qb-creates/LedCube/555LedCube/555LedCube/Cage_Animation.asm

/*
 * Cage_Animation.asm
 *
 *  Created: 4/10/2017 11:21:32 AM
 *   Author: qbake_0
 */ 
 /////////////////////////////////////////////////////////////////////////////////////////////////////////////////////////////////////
Cage:																																;
	ldi Xh, 0x00 ldi Xl, 0xAE																										;
	ldi Byte_1, 0x00 ST X+, Byte_1	ldi Byte_2, 0x00 ST X+, Byte_2	ldi Byte_3, 0x00 ST X+, Byte_3 ldi Byte_4, 0x00 ST X+, Byte_4	;
	ldi Byte_1, 0x00 ST X+, Byte_1	ldi Byte_2, 0x00 ST X+, Byte_2	ldi Byte_3, 0x00 ST X+, Byte_3 ldi Byte_4, 0x00 ST X+, Byte_4	;
	ldi Byte_1, 0x00 ST X+, Byte_1	ldi Byte_2, 0x00 ST X+, Byte_2	ldi Byte_3, 0x00 ST X+, Byte_3 ldi Byte_4, 0x00 ST X+, Byte_4	;
	ldi Byte_1, 0x00 ST X+, Byte_1	ldi Byte_2, 0x00 ST X+, Byte_2	ldi Byte_3, 0x00 ST X+, Byte_3 ldi Byte_4, 0x00 ST X+, Byte_4	;
	ldi Byte_1, 0x00 ST X+, Byte_1	ldi Byte_2, 0x00 ST X+, Byte_2	ldi Byte_3, 0x00 ST X+, Byte_3 ldi Byte_4, 0x00 ST X+, Byte_4	;
	ldi temp_3, 255 ldi counter, 1 call bright																						;
ldi Subtraction4, 0xBE																												;
Cage_loop:																															;
	ldi Xh, 0x00 Mov Xl, Subtraction4 																								;
	ldi Byte_1, 0x01 ST X+, Byte_1	ldi Byte_2, 0x00 ST X+, Byte_2	ldi Byte_3, 0x00 ST X+, Byte_3 ldi Byte_4, 0x00 ST X+, Byte_4	;
	ldi temp_3, 185 ldi counter, 12 call bright																						;
																																	;
	ldi Xh, 0x00 Mov Xl, Subtraction4 																								;
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
	ldi temp_3, 185 ldi counter, 15 call bright																						;
	RET																																;
/////////////////////////////////////////////////////////////////////////////////////////////////////////////////////////////////////
