qb-creates/LedCube/555LedCube/555LedCube/Expand_Animation.asm

/*
 * Expand_Animation.asm
 *
 *  Created: 4/10/2017 11:10:27 AM
 *   Author: qbake_0
 */ 
 ////////////////////////////////////////////////////////////////////////////////////////////////////////////////////////////////
 Expand_4:																														;
			ldi Xh, 0x00																										;
			ldi Xl, 0xAE																										;
			ldi temp, 0x10 ST X+, temp	ldi temp, 0x00 ST X+, temp	ldi temp, 0x00 ST X+, temp	ldi temp, 0x00 ST X+, temp      ;
			ldi temp, 0x00 ST X+, temp	ldi temp, 0x00 ST X+, temp	ldi temp, 0x00 ST X+, temp	ldi temp, 0x00 ST X+, temp      ;
			ldi temp, 0x00 ST X+, temp	ldi temp, 0x00 ST X+, temp	ldi temp, 0x00 ST X+, temp	ldi temp, 0x00 ST X+, temp      ;
			ldi temp, 0x00 ST X+, temp	ldi temp, 0x00 ST X+, temp	ldi temp, 0x00 ST X+, temp	ldi temp, 0x00 ST X+, temp      ;
			ldi temp, 0x00 ST X+, temp	ldi temp, 0x00 ST X+, temp	ldi temp, 0x00 ST X+, temp	ldi temp, 0x00 ST X+, temp      ;
			ldi temp_3, 115 ldi counter, 15 call bright																			;
																																;
			ldi Xh, 0x00																										;
			ldi Xl, 0xAE																										;
			ldi temp, 0x18 ST X+, temp	ldi temp, 0x03 ST X+, temp	ldi temp, 0x00 ST X+, temp	ldi temp, 0x00 ST X+, temp      ;
			ldi temp, 0x18 ST X+, temp	ldi temp, 0x03 ST X+, temp	ldi temp, 0x00 ST X+, temp	ldi temp, 0x00 ST X+, temp      ;
			ldi temp, 0x00 ST X+, temp	ldi temp, 0x00 ST X+, temp	ldi temp, 0x00 ST X+, temp	ldi temp, 0x00 ST X+, temp      ;
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
			ldi temp_3, 115 ldi counter, 10 call bright																			;
																																;
			RET																													;
////////////////////////////////////////////////////////////////////////////////////////////////////////////////////////////////;
