qb-creates/LedCube/555LedCube/555LedCube/Explode_Animation.asm

/*
 * AsmFile3.asm
 *
 *  Created: 4/10/2017 1:16:20 AM
 *   Author: qbake_0
 */ 
 Explode:																																																														;
																									;																																							;
	ldi Xh, 0x00 ldi Xl, 0xBE																																																									;
	ldi Byte_1, 0b00000000 EOR Byte_1, Subtraction4 ST X+, Byte_1	ldi Byte_2, 0b00000000 EOR Byte_2, Subtraction4 ST X+, Byte_2	ldi Byte_3, 0b00000000 EOR Byte_3, Subtraction4 ST X+, Byte_3 ldi Byte_4, 0b00000001 EOR Byte_4, Subtraction4 ST X+, Byte_4	;
	ldi temp_3, 255 ldi counter, 3 call bright																																																				;
																																																																;
	ldi Xh, 0x00 ldi Xl, 0xB6																																																									;
	ldi Byte_1, 0b00000100 eor Byte_1, Subtraction4 ST X+, Byte_1   ldi Byte_2, 0b00000000 eor Byte_2, Subtraction4 ST X+, Byte_2	ldi Byte_3, 0b00000000 eor Byte_3, Subtraction4 ST X+, Byte_3 ldi Byte_4, 0b00000000 eor Byte_4, Subtraction4 ST X+, Byte_4	;
	ldi temp_3, 255 ldi counter, 3 call bright																																																				;
																																																																;
	ldi Xh, 0x00 ldi Xl, 0xBA																																																									;
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
	ldi temp_3, 255 ldi counter, 3 call bright																													;
																																								;
	ldi Xh, 0x00 ldi Xl, 0xB2																																	;
	ldi Byte_1, 0b11111111 eor Byte_1, Subtraction4 ST X+, Byte_1	ldi Byte_2, 0b11111111 eor Byte_2, Subtraction4 ST X+, Byte_2	ldi Byte_3, 0b11111111 eor Byte_3, Subtraction4 ST X+, Byte_3 ldi Byte_4, 0b00000001 eor Byte_4, Subtraction4 ST X+, Byte_4	;
	ldi temp_3, 255 ldi counter, 100 call bright			
	RET																
